elliotf/parametric-carriage-extruder/polyScrewThread.scad

polyScrewThread_r1.scad
